simonnkm/Ambiance/Ambiance-main/WPSSource/WildlifeSource/Core/Src/FLASH.c

/*
 * Name FLASH.c
 * Brief: provides a library to initialize and perform read/write operation to the flash memory
 * Author: Caitlin Bonesio
 * Created: 4/11/25
 * Modified: 4/23/25
 */
#include "FLASH.h"
#include "BOARD.h"

/*
 * These addresses used to sit at 0x1006E000-0x1006FFFF, with SCHEDULEADDRESS
 * (0x1006F000) landing exactly on the BLE stack's own NVM database region
 * (see NVM_START_ADDRESS in Projects/Common/BLE/Modules/NVMDB/Src/nvm_db_conf.c
 * and REGION_NVM in the linker script) - every schedule write and every BLE
 * bonding/GATT persist were silently overwriting each other's flash.
 * Moved to a dedicated block reserved by the linker script
 * (FLASH_APPDATA_SIZE / REGION_APPDATA in STM32WB05KZVX_FLASH.ld) so the
 * build fails instead of silently corrupting data if code ever grows into it.
 */
#define VOLUMEADDRESS  	0x1006C000
#define DCADDRESS 		0x1006C001
#define LOGSADDRESS 	0x1006C800
#define SCHEDULEADDRESS	0x1006E800

#define DCVOLPAGE		88
#define LOGSPAGE		89//logs span LOGSPAGES consecutive pages starting here
#define SCHEDULEPAGE	93

#define FLASHEMPTY 0xFF
#define FLASHPAGESIZE 0x800

#define SCHEDULEEVENTSIZE 8//must be a multiple of 4

//logs get LOGSPAGES pages (instead of the usual 1) so a full 10-week, 2-hour-
//interval deployment fits without ever needing a mid-deployment download.
#define LOGSPAGES 4
#define LOGSCAPACITY ((LOGSPAGES*FLASHPAGESIZE)/SCHEDULEEVENTSIZE)


static int16_t ScheduleSize;
static int16_t LogsSize;
static uint8_t initialized = 0;


/*
 * @function: FLASH_Init()
 * @brief: initialize the flash access library
 * @param: none
 * @return: Init Status, whether the operation failed or succeeded
 */
uint8_t FLASH_Init(){
	if(initialized){return INIT_OK;}
	
	__HAL_FLASH_CLEAR_FLAG(FLASH_FLAG_ALL_ERRORS);
	//find size of schedule
	for(int i = 0; i < FLASHPAGESIZE/SCHEDULEEVENTSIZE; i++){
		if ((uint8_t)(*(uint8_t*)(SCHEDULEADDRESS+(i*SCHEDULEEVENTSIZE))) == FLASHEMPTY ){
			ScheduleSize = i;
			break;
		}
	}
	//find size of logs
	for(int i = 0; i < LOGSCAPACITY; i++){
		if ((uint8_t)(*(uint8_t*)(LOGSADDRESS+(i*SCHEDULEEVENTSIZE))) == FLASHEMPTY ){
			LogsSize = i;
			break;
		}
	}
	FLASH->IRQRAW |= FLASH_FLAG_CMDDONE;
	initialized = 1;
	//load default values into the duty cycle and volume if they are not initialized
	if(FLASH_GetVolume() == FLASHEMPTY ||FLASH_GetDutyCycle() == FLASHEMPTY){
		if(FLASH_GetVolume() == FLASHEMPTY && FLASH_GetDutyCycle() == FLASHEMPTY){
			FLASH_SetDCVol(50, 40);
		}else {
			if(FLASH_GetVolume() == FLASHEMPTY){
				FLASH_SetDCVol(50, FLASH_GetDutyCycle());
			}else {
				FLASH_SetDCVol(FLASH_GetVolume(), 40);
			}
		}
	}
	return INIT_OK;
}

/*
 * @function: FLASH_SetVolume();
 * @brief: edits the volume and duty cycle stored in memory
 * @param: none
 * @return: success status
 */
uint8_t FLASH_SetDCVol(uint8_t volume, uint8_t DC){
	if(!initialized){return 0;}
	FLASH_EraseInitTypeDef erase;
	erase.Page = DCVOLPAGE;
	erase.NbPages = 1;
	erase.TypeErase = FLASH_TYPEERASE_PAGES;
	uint32_t faultypage;
	if(HAL_FLASHEx_Erase(&erase, &faultypage) != HAL_OK){
		/* Page didn't actually erase to all-1s: programming over it now would
		 * silently AND the new value into whatever was already there instead
		 * of writing it (HAL_FLASH_Program can still report HAL_OK even
		 * though the stored volume/duty-cycle ends up wrong), so bail here
		 * instead of proceeding. */
		return 0;
	}
	FLASH_GetVolume();
	FLASH_GetDutyCycle();
	uint32_t data = ((uint32_t)(DC)<<8)+(uint32_t)(volume);
	HAL_StatusTypeDef status = HAL_FLASH_Program(FLASH_TYPEPROGRAM_WORD, VOLUMEADDRESS, data);
	return status == HAL_OK;
}

/*
 * @function: FLASH_GetVolume();
 * @brief: read the volume stored in memory
 * @param: none
 * @return: volume
 */
uint8_t FLASH_GetVolume(){
	if(!initialized){return 0;}
	uint8_t* adr = (uint8_t*)VOLUMEADDRESS;
	return *adr;
}



/*
 * @function: FLASH_GetDutyCycle();
 * @brief: read the volume stored in memory
 * @param: none
 * @return: Duty Cycle
 */
uint8_t FLASH_GetDutyCycle(){
	if(!initialized){return 0;}
	uint8_t* adr = (uint8_t*)DCADDRESS;
	return *adr;
}

/*
 * @function: FLASH_AppendLogs();
 * @brief: Adds a new event entry to the logs
 * @param: none
 * @return: success status
 */
uint8_t FLASH_AppendLogs(scheduleEvent event){
	if(!initialized){return 0;}
	if (LogsSize >= LOGSCAPACITY){
		//logs full (~85 days at the 2-hour logging interval, comfortably past
		//the 10-week deployment): drop the oldest batch and keep logging
		//rather than silently stopping. Should only be reached if the device
		//runs well past its planned deployment length without a download.
		if(!FLASH_ClearLogs()){return 0;}
	}
	uint32_t Data1 = (event.month)|(event.daystart<<8)|(event.start<<16)|(event.stop<<24);
	uint32_t Data2 = (event.daystop)|(event.folder<<8)|(event.track<<16);
	//this isn't blocking code officer I swear! (this is blocking code, to be improved later)
	if(HAL_FLASH_Program(FLASH_TYPEPROGRAM_WORD, LOGSADDRESS+LogsSize*SCHEDULEEVENTSIZE, Data1) != HAL_OK ){
		return 0;
	}
	if(HAL_FLASH_Program(FLASH_TYPEPROGRAM_WORD, LOGSADDRESS+LogsSize*SCHEDULEEVENTSIZE+4, Data2) != HAL_OK ){
		return 0;
	}
	LogsSize++;
	return 1;
}

/*
 * @function: FLASH_GetLogsSize();
 * @brief: returns the size of the logs
 * @param: none
 * @return: Logs size
 */
uint16_t FLASH_GetLogsSize(){
	if(!initialized){return 0;}
	return LogsSize;
}

/*
 * @function: FLASH_ReadLogs();
 * @brief: allows reading the logs that have been stored in flash memory
 * @param: index to read at
 * @return: an schedule event struct at index, null if invalid index
 */
scheduleEvent FLASH_ReadLogs(uint16_t index){
	scheduleEvent event = (scheduleEvent){0, 0, 0, 0, 0, 0};
	if(!initialized){return event;}
	if(index >= 0 && index < LogsSize){
		event.month = *((uint8_t*)(LOGSADDRESS+index*SCHEDULEEVENTSIZE));
		event.daystart = *((uint8_t*)(LOGSADDRESS+index*SCHEDULEEVENTSIZE+1));
		event.start = *((uint8_t*)(LOGSADDRESS+index*SCHEDULEEVENTSIZE+2));
		event.stop = *((uint8_t*)(LOGSADDRESS+index*SCHEDULEEVENTSIZE+3));
		event.daystop = *((uint8_t*)(LOGSADDRESS+index*SCHEDULEEVENTSIZE+4));
		event.folder = *((uint8_t*)(LOGSADDRESS+index*SCHEDULEEVENTSIZE+5));
		event.track = *((uint8_t*)(LOGSADDRESS+index*SCHEDULEEVENTSIZE+6));

	}
	return event;
}

/*
 * @function: FLASH_ClearLogs();
 * @brief: Clears all log entries
 * @param: none
 * @return: success status
 */
uint8_t FLASH_ClearLogs(){
	LogsSize = 0;
	FLASH_EraseInitTypeDef erase;
	erase.Page = LOGSPAGE;
	erase.NbPages = LOGSPAGES;
	erase.TypeErase = FLASH_TYPEERASE_PAGES;
	uint32_t faultypage;
	HAL_StatusTypeDef status = HAL_FLASHEx_Erase(&erase, &faultypage);
	return status == HAL_OK;

}


/*
 * @function: FLASH_AppendSchedule();
 * @brief: Adds a new event entry to the schedule
 * @param: none
 * @return: success status
 */
uint8_t FLASH_AppendSchedule(scheduleEvent event){
	if(!initialized){return 0;}
	if (ScheduleSize >=FLASHPAGESIZE/SCHEDULEEVENTSIZE){return 0;}
	uint32_t Data1 = (event.month)|(event.daystart<<8)|(event.start<<16)|(event.stop<<24);
	uint32_t Data2 = (event.daystop)|(event.folder<<8)|(event.track<<16);
	//this isn't blocking code officer I swear! (this is blocking code)
	uint32_t status = FLASH->IRQRAW;
	status &= FLASH_FLAG_CMDDONE ;
//	while(!(FLASH->IRQRAW&FLASH_FLAG_CMDDONE) && FLASH->IRQRAW&FLASH_FLAG_CMDSTART);
//	FLASH_Program_Burst(SCHEDULEADDRESS+ScheduleSize*SCHEDULEEVENTSIZE,Data1);
//	while(!(FLASH->IRQRAW&FLASH_FLAG_CMDDONE) && FLASH->IRQRAW&FLASH_FLAG_CMDSTART);
//	FLASH_Program_Burst(SCHEDULEADDRESS+ScheduleSize+4*SCHEDULEEVENTSIZE,Data2);
	if(HAL_FLASH_Program(FLASH_TYPEPROGRAM_WORD, SCHEDULEADDRESS+ScheduleSize*SCHEDULEEVENTSIZE, Data1) != HAL_OK ){
		return 0;
	}
	if(HAL_FLASH_Program(FLASH_TYPEPROGRAM_WORD, SCHEDULEADDRESS+ScheduleSize*SCHEDULEEVENTSIZE+4, Data2) != HAL_OK ){
		return 0;
	}
	ScheduleSize++;
	return 1;
}

/*
 * @function: FLASH_GetScheduleSize();
 * @brief: returns the size of the schedule
 * @param: none
 * @return: Schedule size
 */
uint16_t FLASH_GetScheduleSize(){
	if(!initialized){return 0;}
	return ScheduleSize;
}

/*
 * @function: FLASH_ReadSchedule();
 * @brief: allows reading the schedule that have been stored in flash memory
 * @param: index to read at
 * @return: an schedule event struct at index
 */
scheduleEvent FLASH_ReadSchedule(uint16_t index){
	scheduleEvent event = (scheduleEvent){0, 0, 0, 0, 0, 0};
	if(!initialized){return event;}
	if(index >= 0 && index < ScheduleSize){
		uint32_t Data1 = *((uint32_t*)(SCHEDULEADDRESS+index*SCHEDULEEVENTSIZE));
		uint32_t Data2 = *((uint32_t*)(SCHEDULEADDRESS+index*SCHEDULEEVENTSIZE+4));
		event.month = (Data1>>0)&0xFF;
		event.daystart = (Data1>>8)&0xFF;
		event.start = (Data1>>16)&0xFF;
		event.stop = (Data1>>24)&0xFF;
		event.daystop = (Data2>>0)&0xFF;
		event.folder = (Data2>>8)&0xFF;;
		event.track = (Data2>>16)&0xFF;;

	}
	return event;
}

/*
 * @function: FLASH_ClearSchedule();
 * @brief: Clears all Schedule entries
 * @param: none
 * @return: success status
 */
uint8_t FLASH_ClearSchedule(){
	ScheduleSize = 0;
	FLASH_EraseInitTypeDef erase;
	erase.Page = SCHEDULEPAGE;
	erase.NbPages = 1;
	erase.TypeErase = FLASH_TYPEERASE_PAGES;
	uint32_t faultypage;
	HAL_StatusTypeDef status = HAL_FLASHEx_Erase(&erase, &faultypage);
	return status == HAL_OK;
}
